abborg/keyboard/Images/case-bottom-2-9-16.PNG

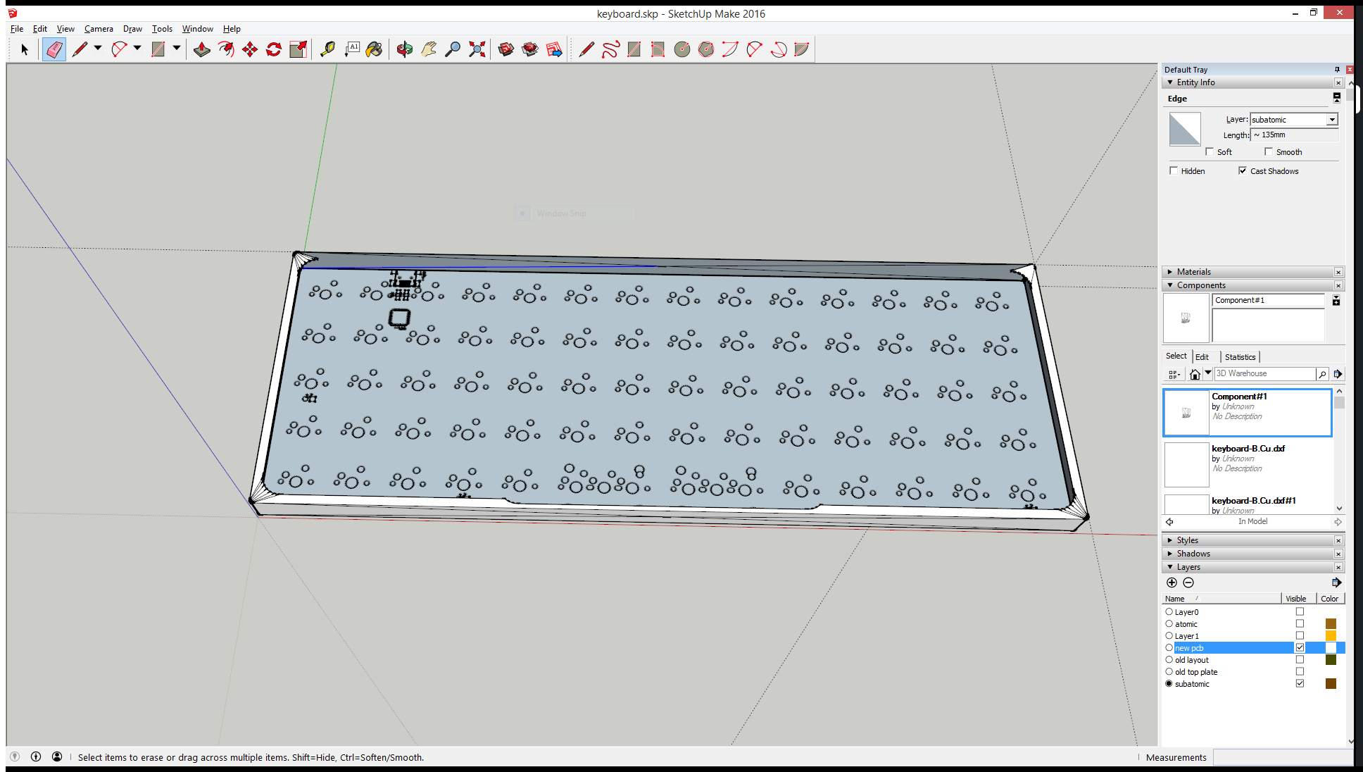
Images/case-bottom-2-9-16.PNG
