abborg/keyboard/Images/case-bottom-2-11-16.PNG

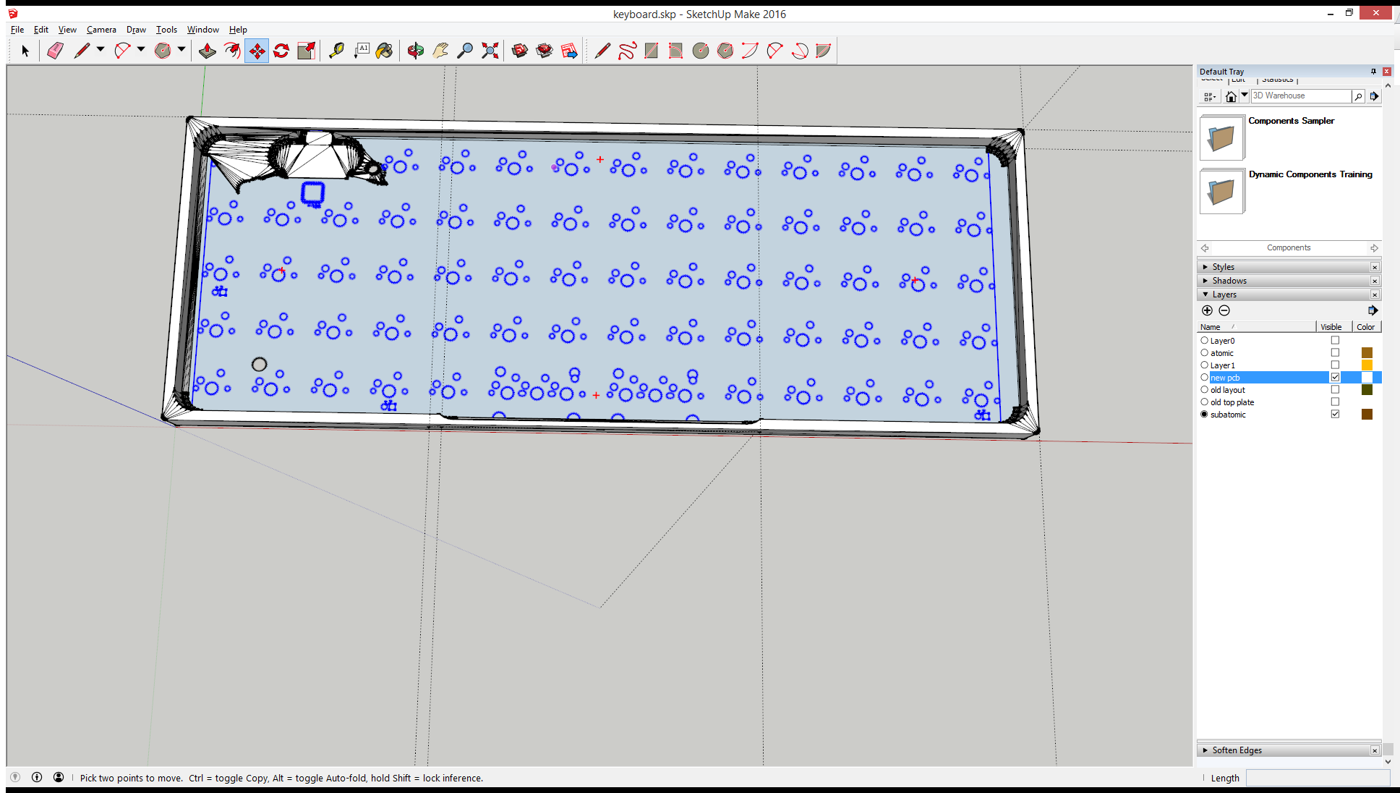
Images/case-bottom-2-11-16.PNG
