abborg/keyboard/KiCad/raccoon.png

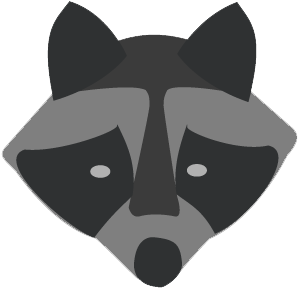
KiCad/raccoon.png
