abborg/keyboard/AutoCAD/slices.stl

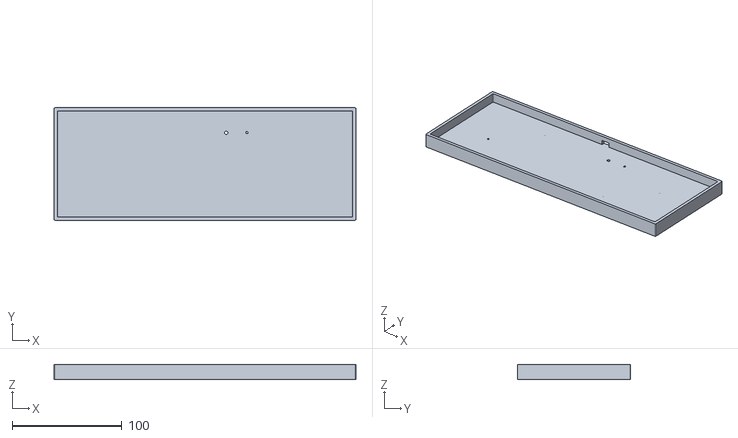
[picture p24: CAD file, 2017-03-04]
AutoCAD/slices.stl
275.0 x 102.5 x 13.5
