abborg/keyboard/AutoCAD/plate-grid.dxf

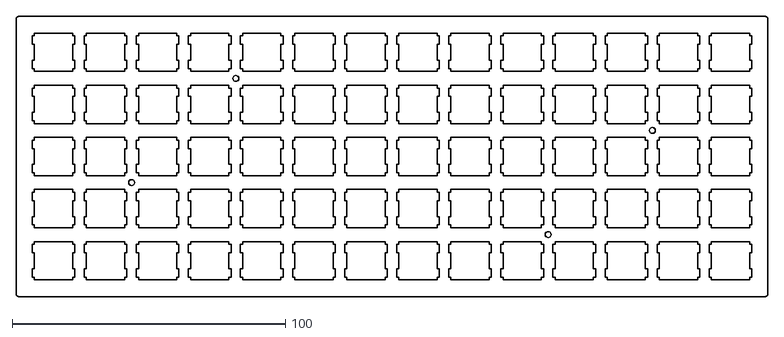
[picture p25: CAD file, 2016-05-31]
AutoCAD/plate-grid.dxf
275.0 x 102.5
