abborg/keyboard/AutoCAD/Plots/casebottomview.dxf

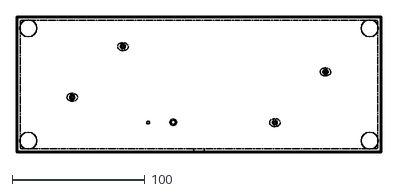
[picture p26: CAD file, 2016-09-12]
AutoCAD/Plots/casebottomview.dxf
275.0 x 102.5
