abborg/keyboard/AutoCAD/plate-MIT.dxf

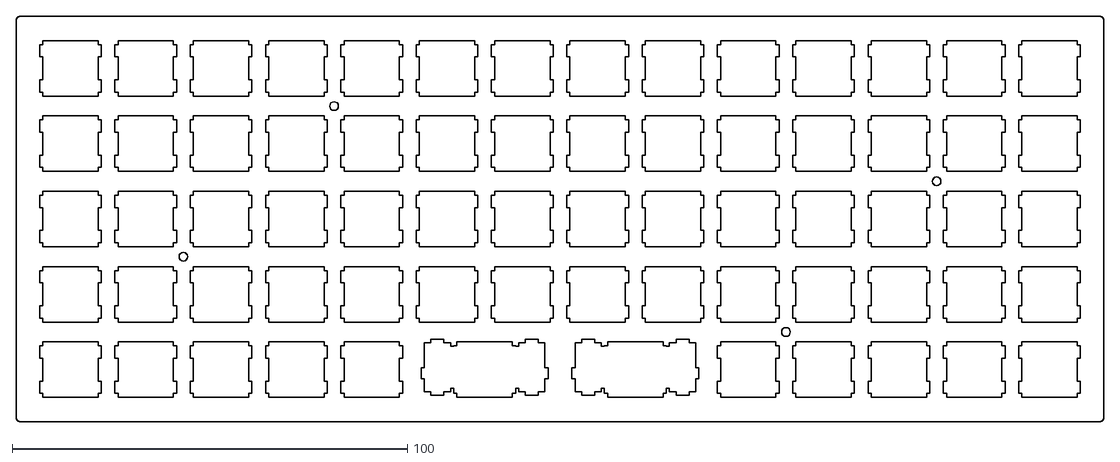
[picture p27: CAD file, 2016-05-31]
AutoCAD/plate-MIT.dxf
275.0 x 102.5
