abborg/keyboard/AutoCAD/Plots/covertopview.dxf

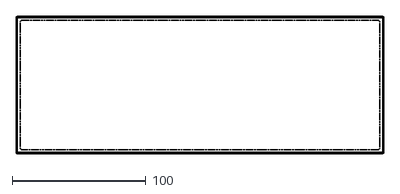
[picture p28: CAD file, 2016-09-12]
AutoCAD/Plots/covertopview.dxf
275.0 x 102.5
