abborg/keyboard/AutoCAD/Plots/coverbottomview.dxf

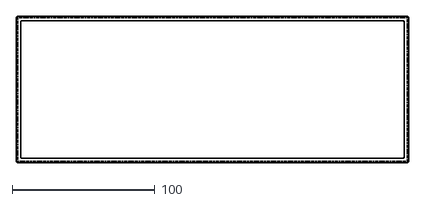
[picture p29: CAD file, 2016-09-12]
AutoCAD/Plots/coverbottomview.dxf
275.0 x 102.5
