abborg/keyboard/AutoCAD/thick_plate-MIT.stl

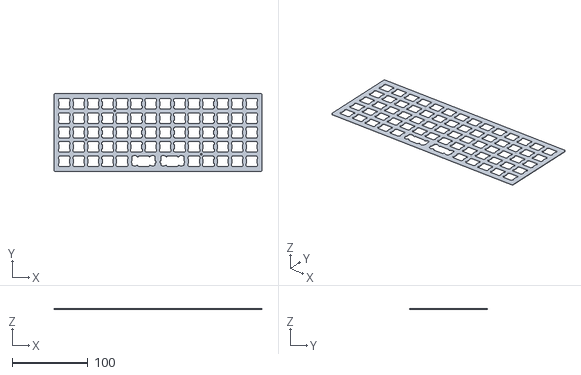
[picture p30: CAD file, 2016-04-21]
AutoCAD/thick_plate-MIT.stl
275.0 x 102.5 x 1.50
