abborg/keyboard/AutoCAD/Plots/casetopview.dxf

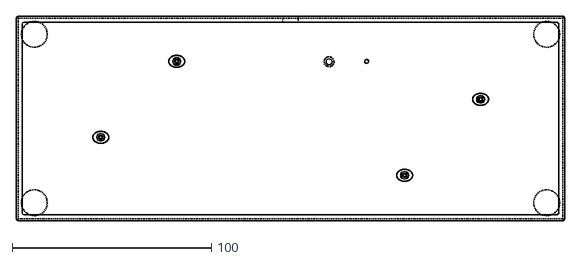
[picture p31: CAD file, 2016-09-12]
AutoCAD/Plots/casetopview.dxf
275.0 x 102.5
